chris3069/BLDC_Project/SW/src/main.hpp

#ifndef Main_h
#define Main_h

#include <Arduino.h>

#include "pin_config.hpp"
#include "button_implementation/button_implementation.hpp"
#include "encoder_implementation/encoder_implementation.hpp"


#include "motor_implementation/motor_implementation.hpp"
#include "motor_implementation/open-loop/open_loop_control.hpp"
#include "motor_implementation/closed-loop/closed_loop_control.hpp"



#endif
