chris3069/BLDC_Project/SW/src/pin_config.hpp

#ifndef Main_Public_h
#define Main_Public_h

                                    // Pin config for Arduino
///////////////////////////////////////////////////////////////////////////////////////////////////////////

#define digital_potiB  13
#define digital_potiA 12

#define IN3  11
#define IN2  10
#define IN1 9

#define reset_pin 8
#define stop_pin 7
#define INH 6

#define HALL2 4
#define HALL1 3
#define HALL0 2

#define IS0 A0
#define IS1 A1
#define IS2 A2

#endif
