chris3069/BLDC_Project/STM_SW/test_mbed/src/motor_implementation/MotorPhase/motorphase.cpp

#include "motorphase.hpp"


// const float sine_wave[120] = {0.0, 0.02639, 0.0527, 0.07887, 0.10482, 0.13047, 0.15576, 0.18062, 0.20497, 0.22876, 0.2519, 0.27435, 0.29602, 0.31688, 0.33685, 0.35588, 0.37392, 0.39092, 0.40682, 0.4216, 0.4352, 0.44758, 0.45872, 0.46858, 0.47713, 0.48436, 0.49023, 0.49474, 0.49787, 0.49961, 0.49996, 0.49891, 0.49648, 0.49266, 0.48746, 0.48091, 0.47302, 0.46381, 0.45331, 0.44154, 0.42855, 0.41435, 0.39901, 0.38255, 0.36503, 0.34648, 0.32698, 0.30656, 0.28528, 0.26322, 0.24041, 0.21694, 0.19287, 0.16825, 0.14317, 0.11769, 0.09187, 0.06581, 0.03956, 0.0132, -0.0132, -0.03956, -0.06581, -0.09187, -0.11769, -0.14317, -0.16825, -0.19287, -0.21694, -0.24041, -0.26322, -0.28528, -0.30656, -0.32698, -0.34648, -0.36503, -0.38255, -0.39901, -0.41435, -0.42855, -0.44154, -0.45331, -0.46381, -0.47302, -0.48091, -0.48746, -0.49266, -0.49648, -0.49891, -0.49996, -0.49961, -0.49787, -0.49474, -0.49023, -0.48436, -0.47713, -0.46858, -0.45872, -0.44758, -0.4352, -0.4216, -0.40682, -0.39092, -0.37392, -0.35588, -0.33685, -0.31688, -0.29602, -0.27435, -0.2519, -0.22876, -0.20497, -0.18062, -0.15576, -0.13047, -0.10482, -0.07887, -0.0527, -0.02639, 0.0};
// const int8_t block_commutation[6] = {1, 0, 0, 1, 2, 2};  

// const int8_t block_commutation_P2[6] = {2, 2, 1, 0, 0, 1}; 
// const int8_t block_commutation_P3[6] = {0, 1, 2, 2, 1, 0};  

MotorPhase::MotorPhase(uint8_t motorphase)
    :switching_frequency(50)
{
    switch (motorphase)
    {
        case 1:
            INH = new DigitalOut(D6);
            IN = new PwmOut(D9);
            break;
        case 2:
            INH = new DigitalOut(PB_15);
            IN = new PwmOut(D10);
            break;
        case 3:
            INH = new DigitalOut(PB_14);
            IN = new PwmOut(D11);
            break; 
    }
    IN->period_us(50);
}

void MotorPhase::previous_phase(void)
{
    next_step(-1);
}

void MotorPhase::next_phase(void)
{
    next_step(1);
}

void MotorPhase::resume(void)
{
    INH->write(1);
    IN->resume();
}

void MotorPhase::suspend(void)
{
    INH->write(0);
    IN->suspend();
}

void MotorPhase::power_current_state(int8_t direction, uint8_t current_position)
{
    // INH->write(1)
    float pwm_level = getPWM_Level(direction, current_position);
    IN->write(0.4 * pwm_level); // 0,5 vorsichtshalber mal
}

MotorPhase::~MotorPhase()
{
    delete IN;
    delete INH;
}
