chris3069/BLDC_Project/STM_SW/test_mbed/src/encoder_implementation/encoder_implementation.hpp

#ifndef encoder_implementation_h
#define encoder_implementation_h


class Encoder_Implementation
{
  public:
    // virtual void motor_control(float velocity) = 0;
    // virtual void start_motor_control(void) = 0;
    // virtual void quit_motor_control(void) = 0;
    Encoder_Implementation() {};
    virtual ~Encoder_Implementation() {};
};


// float getTargetSpeed(void);
// void reset_target_speed(void);

#endif
