chris3069/BLDC_Project/STM_SW/test_mbed/src/button_implementation/button_implementation.cpp

#include "button_implementation.hpp"

// #include "OneButton.h"
// #include "pin_config.hpp"

// OneButton reset_button(reset_pin, true, false);

// void init_button(void (*pReset_Target_speed)())
// {
//   reset_button.attachClick(pReset_Target_speed);
// }


// void read_swtich(void (*pStart_motor)())
// {
// 	bool start_pushbutton = digitalRead(stop_pin);
// 	if (start_pushbutton == true)
// 	{
// 	  Serial.println("Switch pressed -> Start Motor Control");
// 	  pStart_motor();
// 	}
// }




// void read_buttons(void (*pStart_motor)())
// {

//   read_swtich(pStart_motor);
//   reset_button.tick();

// }
